akshatnerella/open-deck/v0/firmware/diagnostics/oled_logo_test/grok_logo_bitmap.h

// 64x64 1-bit bitmap, generated from terminal-badge.dxf geometry
#define LOGO_WIDTH 64
#define LOGO_HEIGHT 64
static const unsigned char PROGMEM logo_bitmap[] = {
  0x00, 0x00, 0x00, 0x00, 0x00, 0x00, 0x00, 0x00, 0x00, 0x00, 0x00, 0x00,
  0x00, 0x00, 0x00, 0x00, 0x00, 0x00, 0x00, 0x00, 0x00, 0x00, 0x00, 0x00,
  0x00, 0x00, 0x00, 0x00, 0x00, 0x00, 0x00, 0x00, 0x00, 0x00, 0x00, 0x00,
  0x00, 0x00, 0x00, 0x00, 0x00, 0x00, 0x00, 0x00, 0x00, 0x00, 0x00, 0x00,
  0x00, 0x03, 0xFF, 0xFF, 0xFF, 0xFF, 0xC0, 0x00, 0x00, 0x07, 0xFF, 0xFF,
  0xFF, 0xFF, 0xE0, 0x00, 0x00, 0x0F, 0xFF, 0xFF, 0xFF, 0xFF, 0xF0, 0x00,
  0x00, 0x1F, 0xFF, 0xFF, 0xFF, 0xFF, 0xF8, 0x00, 0x00, 0x3E, 0x00, 0x00,
  0x00, 0x00, 0x7C, 0x00, 0x00, 0x7C, 0x00, 0x00, 0x00, 0x00, 0x3E, 0x00,
  0x00, 0xF8, 0x00, 0x00, 0x00, 0x00, 0x1F, 0x00, 0x01, 0xF0, 0x00, 0x00,
  0x00, 0x00, 0x0F, 0x80, 0x03, 0xE0, 0x00, 0x00, 0x00, 0x00, 0x07, 0xC0,
  0x03, 0xC0, 0x00, 0x00, 0x00, 0x00, 0x03, 0xC0, 0x03, 0xC0, 0x00, 0x00,
  0x00, 0x00, 0x03, 0xC0, 0x03, 0xC0, 0x00, 0x00, 0x00, 0x00, 0x03, 0xC0,
  0x03, 0xC3, 0x00, 0x00, 0x00, 0x00, 0x03, 0xC0, 0x03, 0xC3, 0x80, 0x00,
  0x00, 0x00, 0x03, 0xC0, 0x03, 0xC3, 0xC0, 0x00, 0x00, 0x00, 0x03, 0xC0,
  0x03, 0xC3, 0xE0, 0x00, 0x00, 0x00, 0x03, 0xC0, 0x03, 0xC1, 0xF8, 0x00,
  0x00, 0x00, 0x03, 0xC0, 0x03, 0xC0, 0xFC, 0x00, 0x00, 0x00, 0x03, 0xC0,
  0x03, 0xC0, 0x3E, 0x00, 0x00, 0x00, 0x03, 0xC0, 0x03, 0xC0, 0x1F, 0x00,
  0x00, 0x00, 0x03, 0xC0, 0x03, 0xC0, 0x07, 0x80, 0x00, 0x00, 0x03, 0xC0,
  0x03, 0xC0, 0x03, 0xE0, 0x00, 0x00, 0x03, 0xC0, 0x03, 0xC0, 0x01, 0xF0,
  0x00, 0x00, 0x03, 0xC0, 0x03, 0xC0, 0x00, 0x78, 0x00, 0x00, 0x03, 0xC0,
  0x03, 0xC0, 0x00, 0x3C, 0x00, 0x00, 0x03, 0xC0, 0x03, 0xC0, 0x00, 0x0F,
  0x00, 0x00, 0x03, 0xC0, 0x03, 0xC0, 0x00, 0x1F, 0x00, 0x00, 0x03, 0xC0,
  0x03, 0xC0, 0x00, 0x3C, 0x00, 0x00, 0x03, 0xC0, 0x03, 0xC0, 0x00, 0x78,
  0x00, 0x00, 0x03, 0xC0, 0x03, 0xC0, 0x01, 0xF0, 0x00, 0x00, 0x03, 0xC0,
  0x03, 0xC0, 0x03, 0xE0, 0x00, 0x00, 0x03, 0xC0, 0x03, 0xC0, 0x0F, 0x80,
  0x00, 0x00, 0x03, 0xC0, 0x03, 0xC0, 0x1F, 0x00, 0x3F, 0xFF, 0x03, 0xC0,
  0x03, 0xC0, 0x3E, 0x00, 0x1F, 0xFF, 0x03, 0xC0, 0x03, 0xC0, 0xFC, 0x00,
  0x1F, 0xFF, 0x03, 0xC0, 0x03, 0xC1, 0xF0, 0x00, 0x3F, 0xFF, 0x03, 0xC0,
  0x03, 0xC3, 0xE0, 0x00, 0x1F, 0xFF, 0x03, 0xC0, 0x03, 0xC3, 0xC0, 0x00,
  0x00, 0x00, 0x03, 0xC0, 0x03, 0xC3, 0x80, 0x00, 0x00, 0x00, 0x03, 0xC0,
  0x03, 0xC3, 0x00, 0x00, 0x00, 0x00, 0x03, 0xC0, 0x03, 0xC0, 0x00, 0x00,
  0x00, 0x00, 0x03, 0xC0, 0x03, 0xC0, 0x00, 0x00, 0x00, 0x00, 0x03, 0xC0,
  0x03, 0xC0, 0x00, 0x00, 0x00, 0x00, 0x03, 0xC0, 0x03, 0xE0, 0x00, 0x00,
  0x00, 0x00, 0x07, 0xC0, 0x01, 0xF0, 0x00, 0x00, 0x00, 0x00, 0x0F, 0x80,
  0x00, 0xF8, 0x00, 0x00, 0x00, 0x00, 0x1F, 0x00, 0x00, 0x7C, 0x00, 0x00,
  0x00, 0x00, 0x3E, 0x00, 0x00, 0x3E, 0x00, 0x00, 0x00, 0x00, 0x7C, 0x00,
  0x00, 0x1F, 0xFF, 0xFF, 0xFF, 0xFF, 0xF8, 0x00, 0x00, 0x0F, 0xFF, 0xFF,
  0xFF, 0xFF, 0xF0, 0x00, 0x00, 0x07, 0xFF, 0xFF, 0xFF, 0xFF, 0xE0, 0x00,
  0x00, 0x03, 0xFF, 0xFF, 0xFF, 0xFF, 0xC0, 0x00, 0x00, 0x00, 0x00, 0x00,
  0x00, 0x00, 0x00, 0x00, 0x00, 0x00, 0x00, 0x00, 0x00, 0x00, 0x00, 0x00,
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
};
